penguintutor/modelrailway-point-controller/electronics/solenoid-demo/solenoid-demo/solenoid-demo.pdf

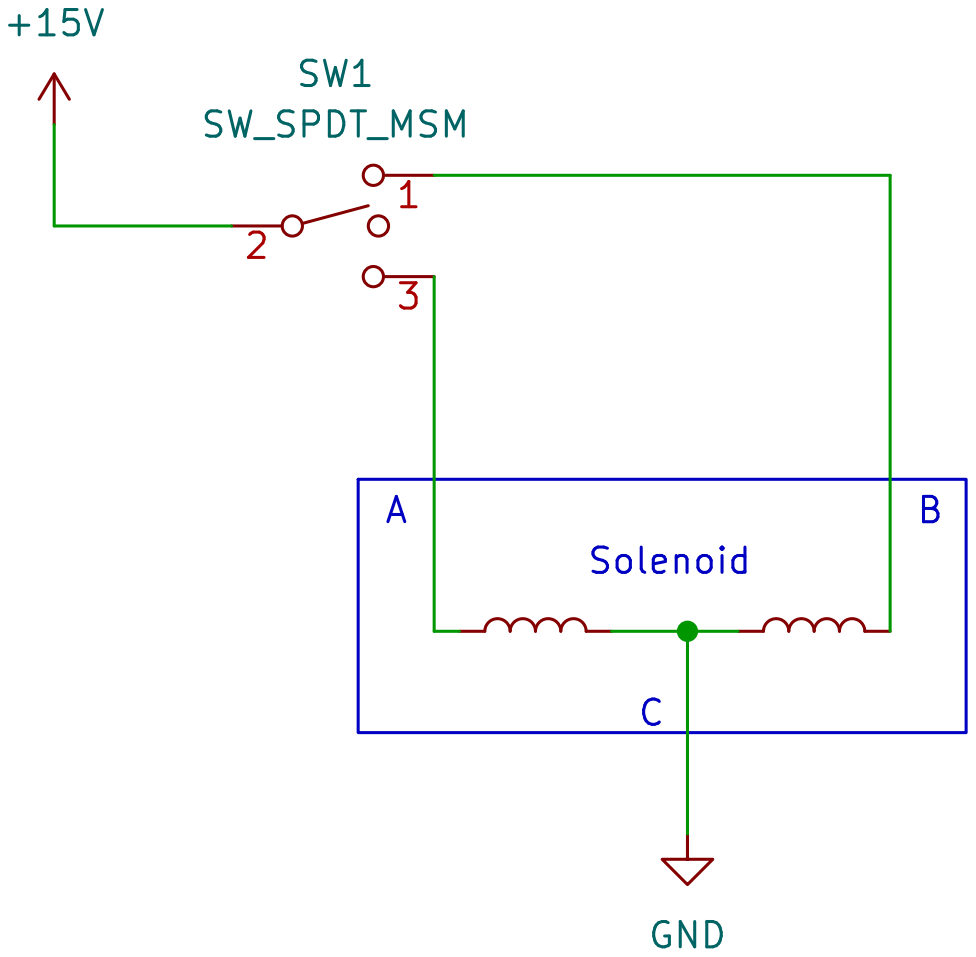
[picture p9: page 1]

Id: 1/1 Title: File: solenoid-demo.kicad_sch Sheet: /
