penguintutor/modelrailway-point-controller/electronics/point-controller/plots/point-controller-B_Cu.pdf

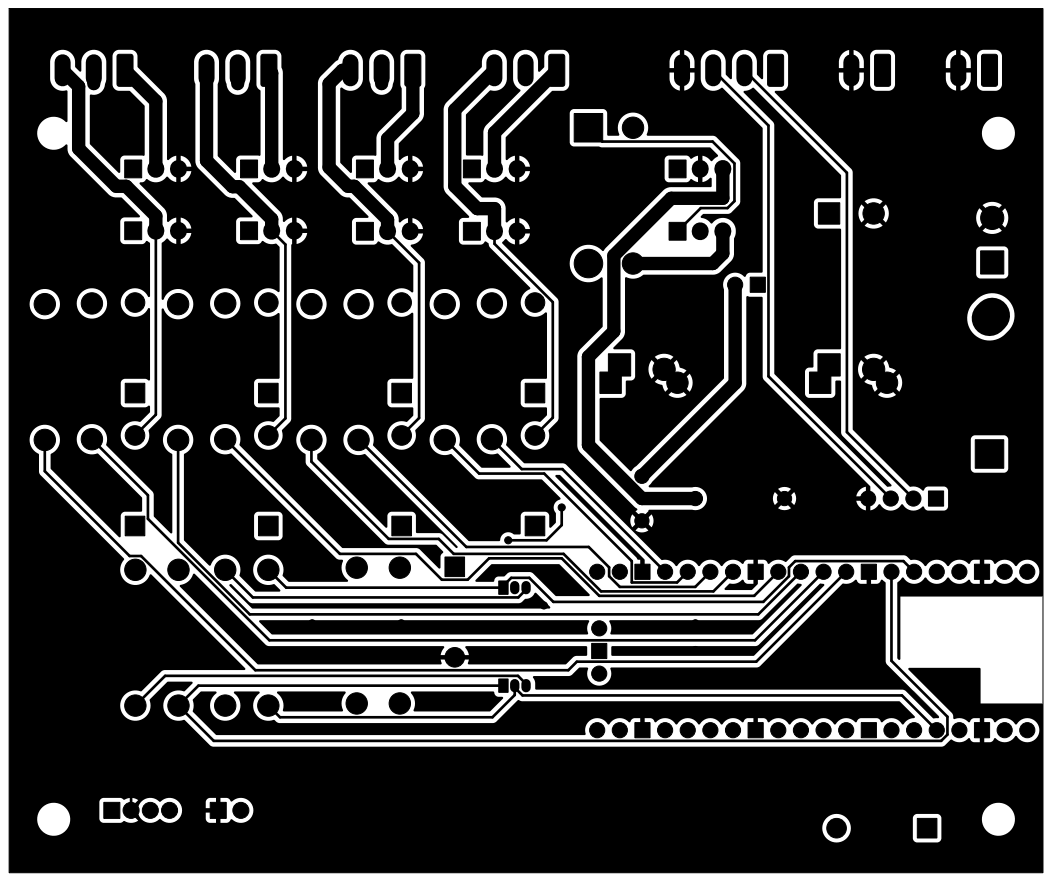
[picture p19: page 1]
