penguintutor/modelrailway-point-controller/electronics/point-controller/plots/point-controller-B_Mask.pdf

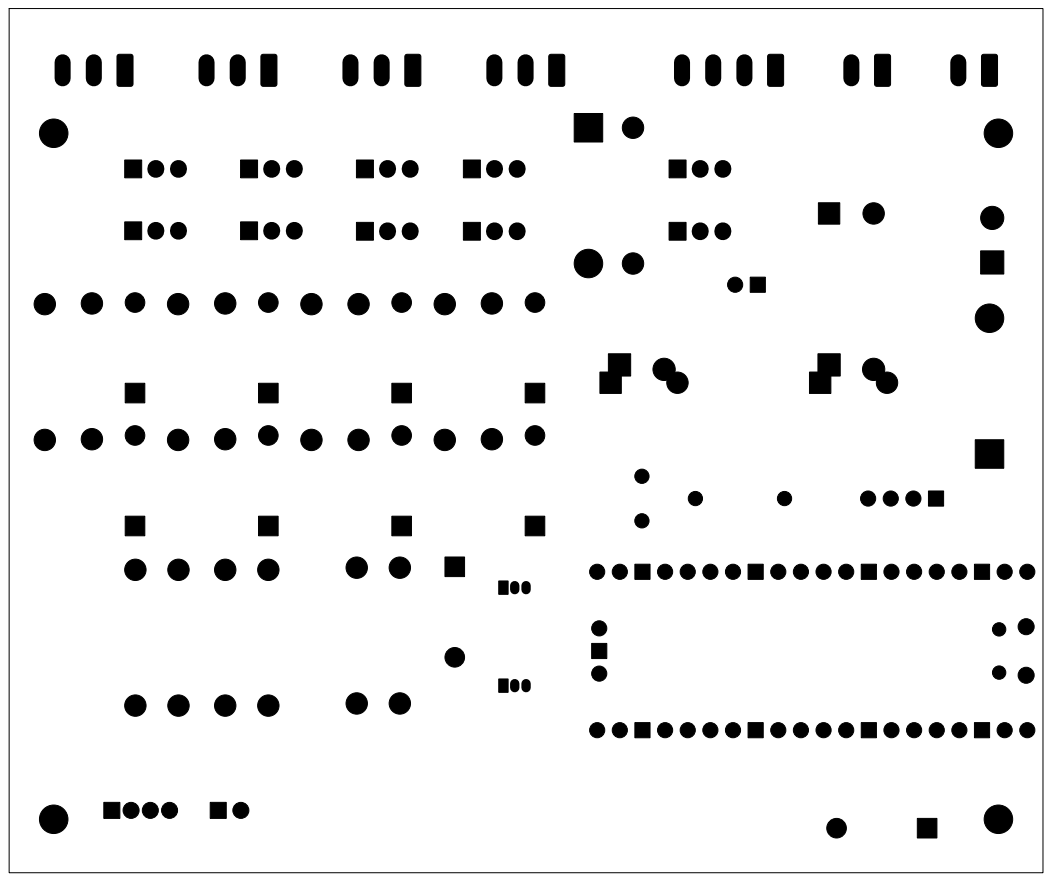
[picture p20: page 1]
