penguintutor/modelrailway-point-controller/electronics/point-controller/plots/point-controller-Capacitor Discharge.pdf

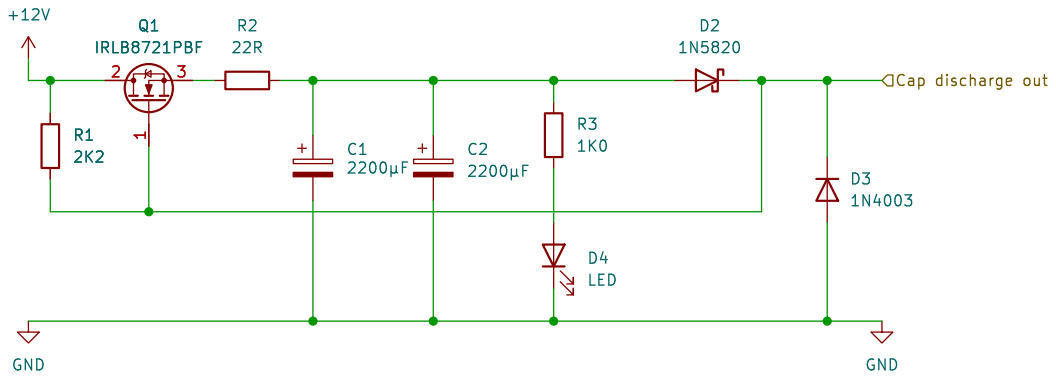
[picture p21: page 1]
