penguintutor/modelrailway-point-controller/electronics/point-controller/plots/point-controller-F_Cu.pdf

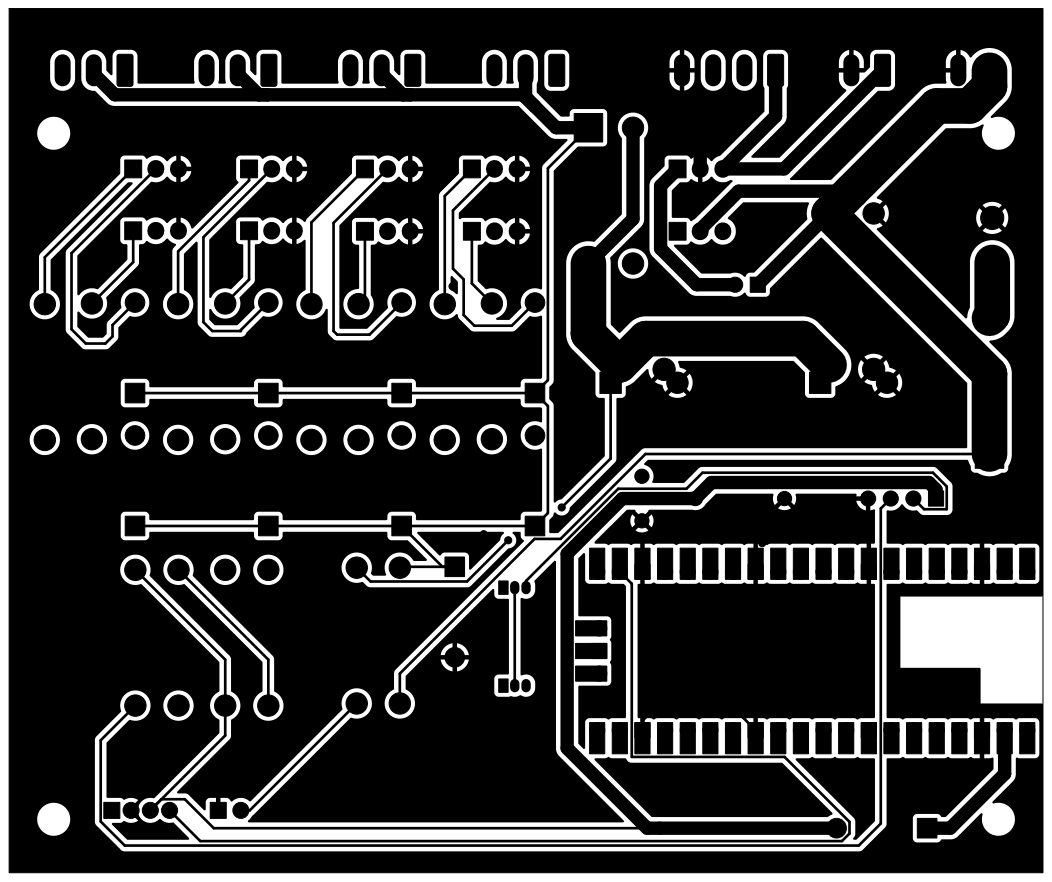
[picture p22: page 1]
