penguintutor/modelrailway-point-controller/electronics/point-controller/plots/point-controller-F_Mask.pdf

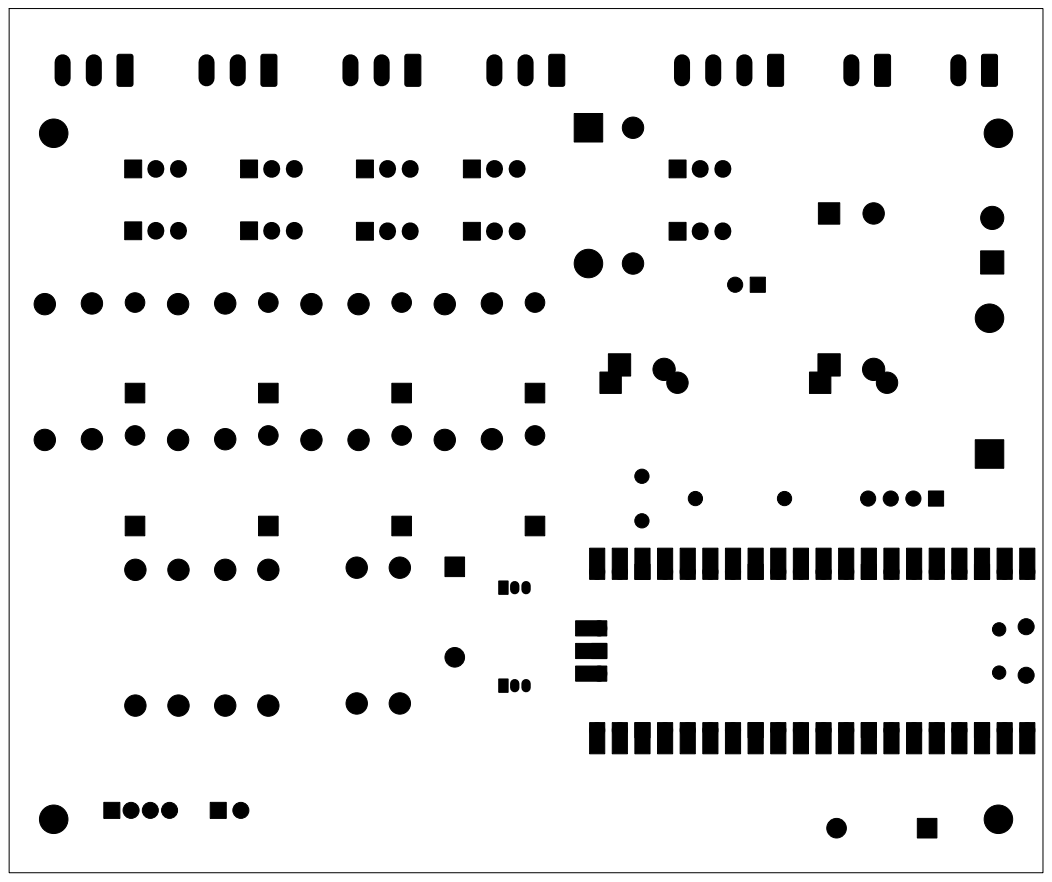
[picture p23: page 1]
