penguintutor/modelrailway-point-controller/electronics/point-controller/plots/point-controller-F_Silkscreen.pdf

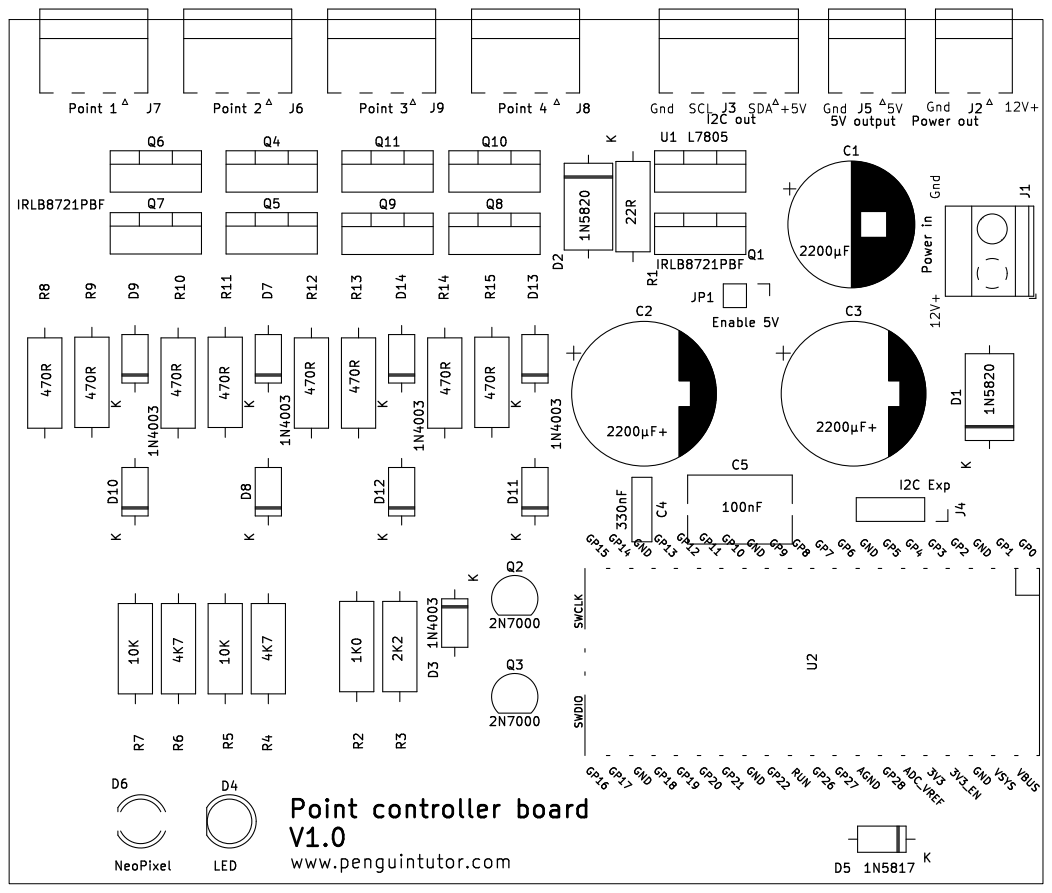
[picture p24: page 1]
